RupinMittal/Autonomous-Maze-Robot/Code-SRC/Src/controller.c

/*
 * controller.c
 *
 *  Created on: Sep 27, 2020
 *      Author: Tyler Price
 */

#include "main.h"
#include "controller.h"
#include "pid.h"

/*
 * We recommend you implement this function so that move(1) will move your rat 1 cell forward.
 */
void move(int8_t n)
{
	/*
	 * For assignment 3.1: Don't worry about implementing this yet
	 * For assignment 3.2: This function should set the distance and angle goals appropriately for PID (hint: using the setGoal functions in pid.c)
	 * and wait until the error becomes sufficiently small and persistent before exiting. This function should NOT exit before then.
	 *
	 * HINT: Use a while loop to wait until the rat has moved the desired distance
	 *
	 * You should also call resetPID before exiting this function so your rat is ready for the next instruction.
	 */

	resetPID();
	setPIDGoalA(0);
	setPIDGoalD(n * -582);		//the difference in encoder counts for a 90 degree turn is approximately 600 encoder counts. (as I measured it using live expressions for encoder counts)
	while (PIDdone() != 1)		//wait until turn is complete
		;
	resetPID();					//and then reset
}

/*
 * We recommend you implement this function so that turn(1) turns your rat 90 degrees in your positive rotation
 * direction and turn(-1) turns the other way.
 */
void turn(int8_t n)
{
	/*
	 * For assignment 3.1: Don't worry about implementing this yet
	 * For assignment 3.2: This function should set the distance and angle goals appropriately for PID (hint: using the setGoal functions in pid.c)
	 * and wait until the error becomes sufficiently small and persistent before exiting. This function should NOT exit before then.
	 *
	 * HINT: Use a while loop to wait until the turn is complete
	 *
	 * You should also call resetPID before exiting this function so your rat is ready for the next instruction.
	 */

	resetPID();
	setPIDGoalA(n * 605);		//the difference in encoder counts for a 90 degree turn is approximately 620 encoder counts. (as I measured it using live expressions for encoder counts)
	setPIDGoalD(0);
	while (PIDdone() != 1)		//wait until turn is complete
		;
	resetPID();					//and then reset
}
