RupinMittal/Autonomous-Maze-Robot/Code-SRC/Inc/controller.h

/*
 * controller.h
 *
 *  Created on: Sep 27, 2020
 *      Author: Tyler Price
 */

#ifndef INC_CONTROLLER_H_
#define INC_CONTROLLER_H_

#include "main.h"

void move(int8_t n);
void turn(int8_t n);

#endif /* INC_CONTROLLER_H_ */
