RupinMittal/Autonomous-Maze-Robot/Code-SRC/Inc/encoders.h

/*
 * encoders.h
 *
 *  Created on: Sep 27, 2020
 *      Author: Tyler Price
 */

#ifndef INC_ENCODERS_H_
#define INC_ENCODERS_H_

int16_t getRightEncoderCounts();
int16_t getLeftEncoderCounts();
void resetEncoders();

#endif /* INC_ENCODERS_H_ */
